GrantMoe/robocar-tx/hw/tx-pcb/tx-pcb.kicad_sch

## KiCad design hw/tx-pcb/tx-pcb.kicad_sch (2022-01-03)

Schematic: tx-pcb.kicad_sch

Parts:
J1: ST_IN
J2: TH_IN
J3: CH_3
J4: CH_4

Connections:
3v: J1.1, J2.1, J3.1, J4.1
CH_1: J1.2
CH_2: J2.2
CH_3: J3.2
CH_4: J4.2
GND: J1.3, J2.3, J3.3, J4.3

Notes on the sheet:
Check RGB order, polarity
